noobychris/vga-sync-combiner-audi-rnse/kicad_files/3dmodels/61300511121.stp

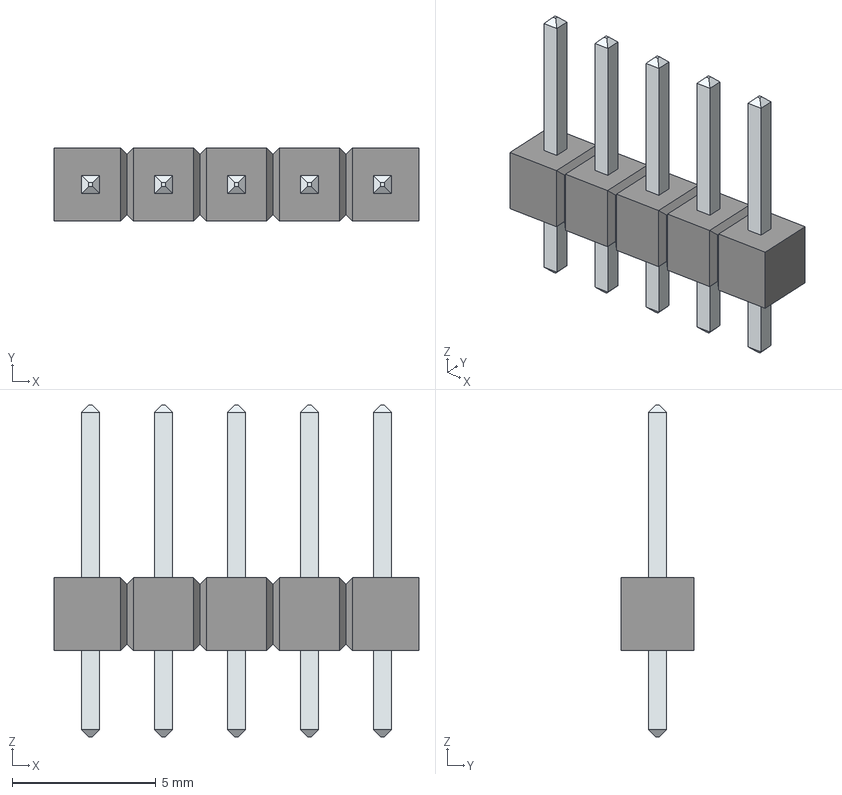
[picture p20: CAD file, 2026-06-04]
kicad_files/3dmodels/61300511121.stp
12.7 x 2.54 x 11.5 mm
LeadsArray
